DJTobias/Cherry-Autonomous-Racecar/3DPrinted/car_front_headlights.PNG

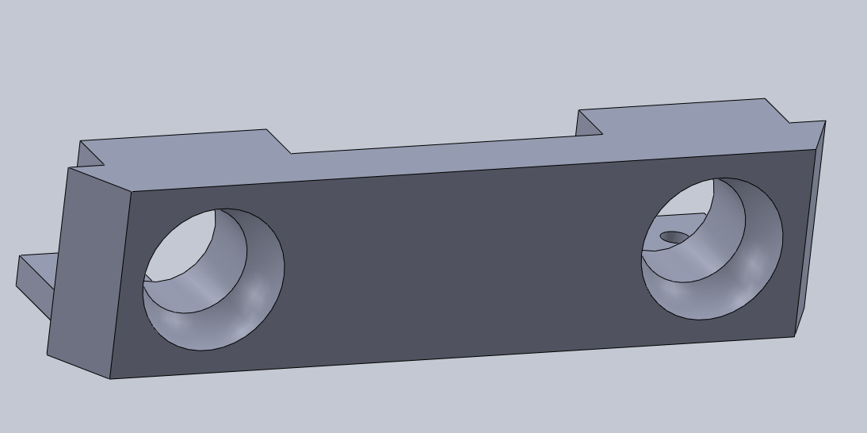
3DPrinted/car_front_headlights.PNG
