DJTobias/Cherry-Autonomous-Racecar/3DPrinted/car_main_platform.PNG

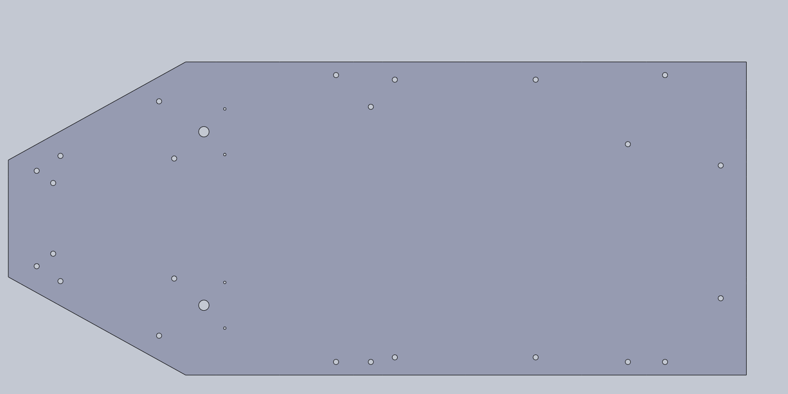
3DPrinted/car_main_platform.PNG
