DJTobias/Cherry-Autonomous-Racecar/3DPrinted/car_RealSenseR200_mount.JPG

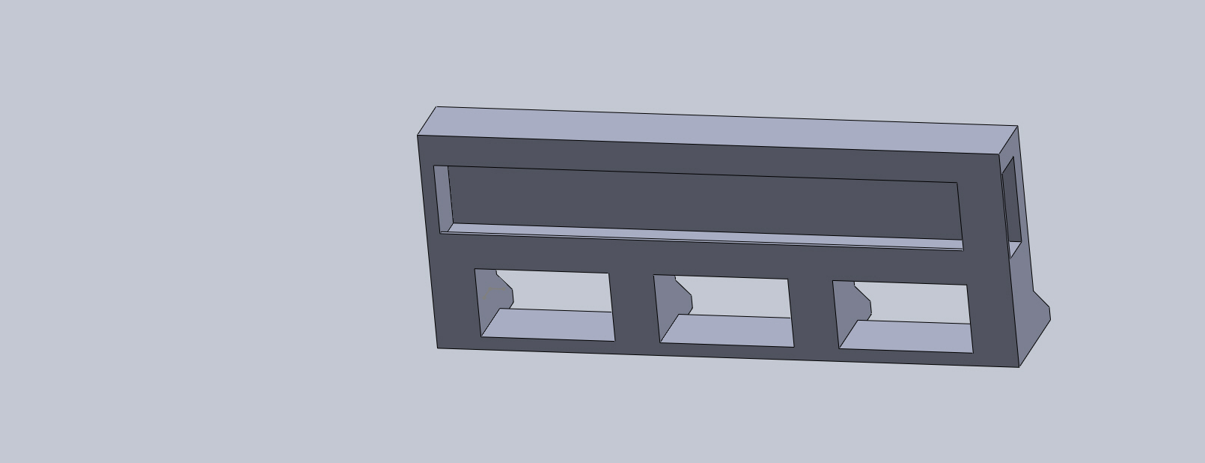
3DPrinted/car_RealSenseR200_mount.JPG
