DJTobias/Cherry-Autonomous-Racecar/3DPrinted/car_sige_turnsignal.PNG

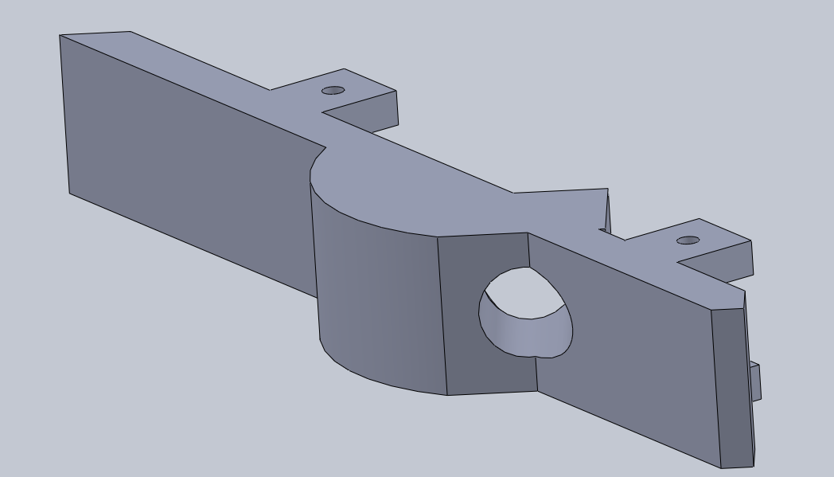
3DPrinted/car_sige_turnsignal.PNG
