DJTobias/Cherry-Autonomous-Racecar/3DPrinted/car_top_panel.JPG

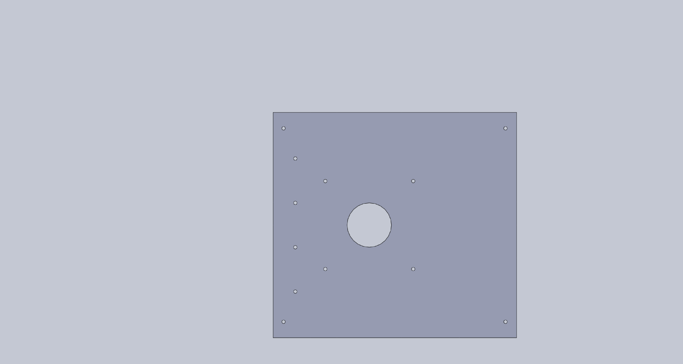
3DPrinted/car_top_panel.JPG
