DJTobias/Cherry-Autonomous-Racecar/3DPrinted/car_webcam_panel.JPG

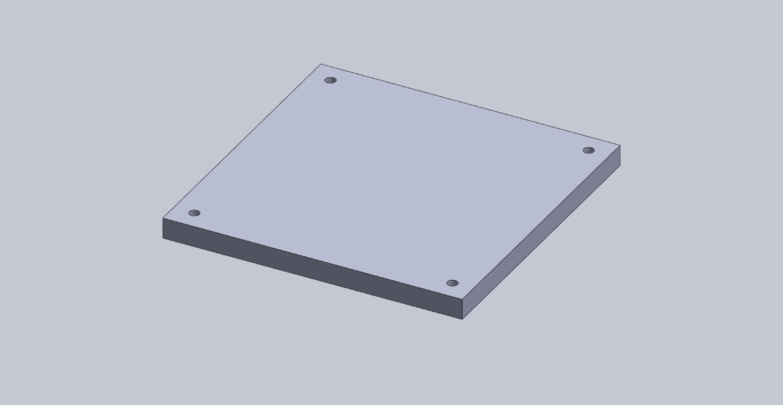
3DPrinted/car_webcam_panel.JPG
