DJTobias/Cherry-Autonomous-Racecar/3DPrinted/car_XP18000_battery_holder.JPG

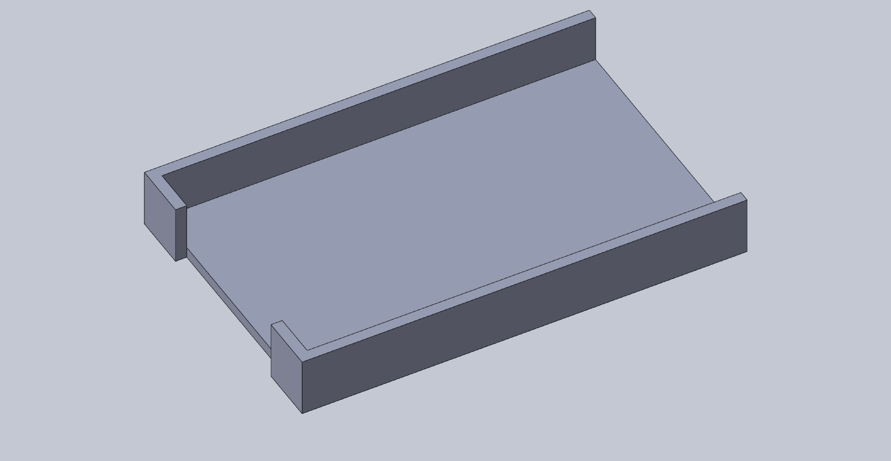
3DPrinted/car_XP18000_battery_holder.JPG
