DJTobias/Cherry-Autonomous-Racecar/pictures/rosgraph.png

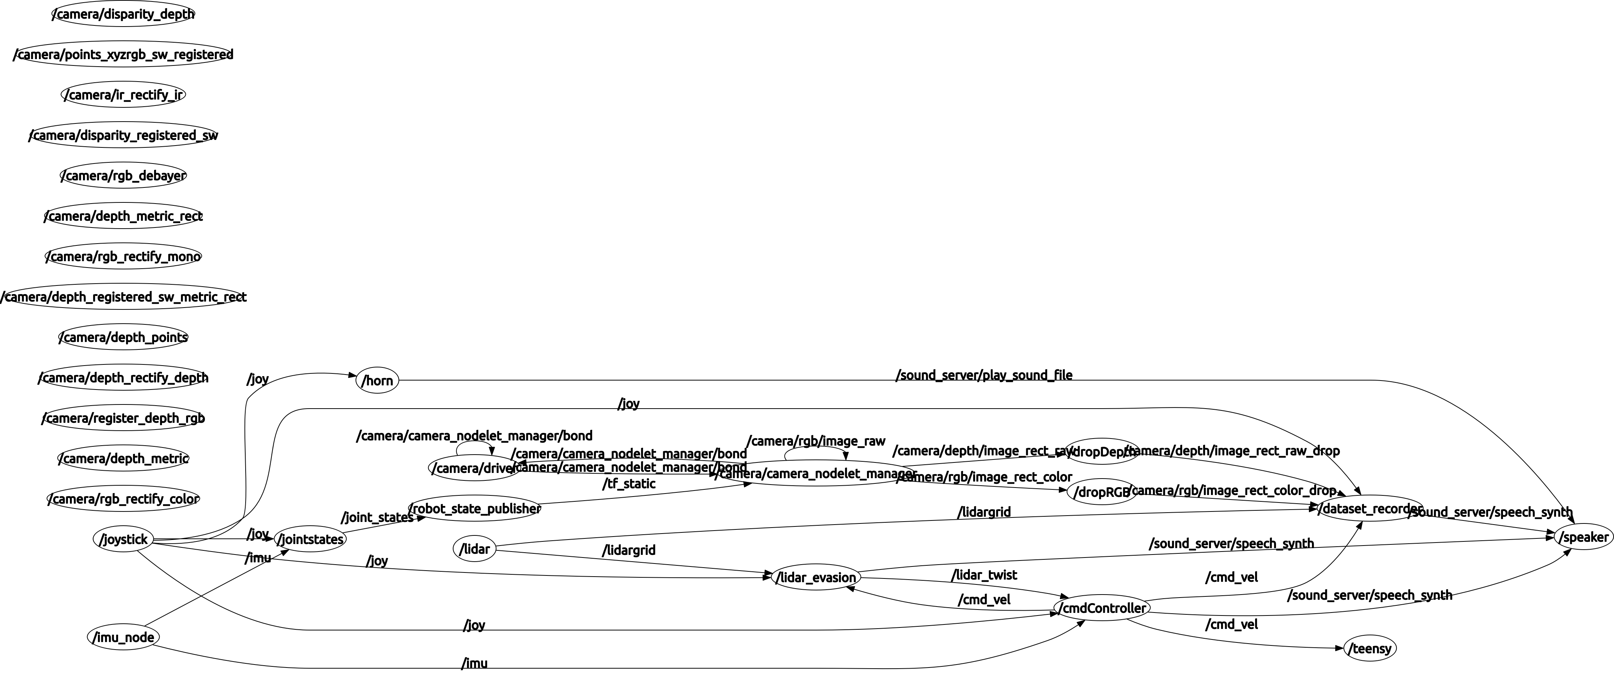
pictures/rosgraph.png
